89Mods/6507SBC/Programs/psg_test/test.asm

.feature string_escapes
.feature org_per_seg
.feature c_comments

PORT1_OUT = $0201
PORT2_OUT = $0202
PORT_IN   = $0208

mem_start = $80
port1_shadow = mem_start
port2_shadow = mem_start+1
temp = mem_start+2
ptr_lo = mem_start+3
ptr_hi = mem_start+4
temp2 = mem_start+5

.segment "CODE"
NMI:
	rti
IRQ:
	rti
RESET:
	ldx #$FF
	txs
	lda #0
	sta port2_shadow
	sta temp
	
	lda #(vgm_data&255)
	sta ptr_lo
	lda #((vgm_data/256)&255)
	sta ptr_hi
	
	lda #64
	sta PORT1_OUT
	sta port1_shadow
	
	jsr init_psg
	
loop:
	lda port2_shadow
	eor #1
	sta PORT2_OUT
	sta port2_shadow
	ldx #0
	lda (ptr_lo,X)
	cmp #$50
	beq vgm_note
	cmp #$61
	beq vgm_delay
	cmp #$63
	beq vgm_20ms
	cmp #$66
	beq end_song
	jmp end_switch
vgm_note:
	jsr inc_pointer
	lda (ptr_lo,X)
	jsr psg_write
	jmp end_switch
vgm_delay:
	jsr inc_pointer
	lda (ptr_lo,X)
	sta temp
	jsr inc_pointer
	lda (ptr_lo,X)
	sta temp2
	
	lda temp2
	lsr
	sta temp2
	lda temp
	ror
	sta temp
vgm_delay_loop:
	nop
	nop
	nop
	nop
	nop
	nop
	nop
	nop
	nop
	lda temp
	sec
	sbc #1
	sta temp
	lda temp2
	sbc #0
	sta temp2
	lda #0
	ora temp
	ora temp2
	bne vgm_delay_loop
	jmp end_switch
vgm_20ms:
	lda #$72
	sta temp
	lda #$03
	sta temp2
	jmp vgm_delay_loop
end_switch:

	jsr inc_pointer
	jmp loop
	
end_song:
	lda #%11111001
	jsr psg_write
	lda #%11111011
	jsr psg_write
	lda #%11111101
	jsr psg_write
	lda #%11111111
	jsr psg_write
halt:
	nop
	lda #%11111001
	jsr psg_write
	lda port2_shadow
	eor #1
	sta PORT2_OUT
	sta port2_shadow
	lda #31
	jsr long_delay
	lda PORT_IN
	and #1
	bne halt
	jmp RESET
	
inc_pointer:
	lda ptr_lo
	clc
	adc #1
	sta ptr_lo
	lda ptr_hi
	adc #0
	sta ptr_hi
	rts

init_psg:
	lda #%11111001
	jsr psg_write
	lda #%11111011
	jsr psg_write
	lda #%11111101
	jsr psg_write
	lda #%11111111
	jsr psg_write
	
	lda #64
	jsr long_delay
	
	lda #%00110001
	jsr psg_write
	lda #%00100000
	jsr psg_write
	
	lda #%00011001
	jsr psg_write
	lda #16
	jsr long_delay
	lda #%11111001
	jsr psg_write
	lda #4
	jsr long_delay
	lda #%00011001
	jsr psg_write
	lda #16
	jsr long_delay
	lda #%11111001
	jsr psg_write
	
	lda #64
	jsr long_delay
	rts

psg_write:
	pha
	lda port1_shadow
	and #%11110000
	sta port1_shadow
	pla
	pha
	and #%00001111
	ora port1_shadow
	sta PORT1_OUT
	sta port1_shadow
	
	lda port2_shadow
	and #%00001111
	sta port2_shadow
	pla
	and #%11110000
	ora port2_shadow
	sta PORT2_OUT
	sta port2_shadow
	
	lda port1_shadow
	and #%10111111
	sta PORT1_OUT
	nop
	nop
	nop
	nop
	nop
	nop
	ora #%01000000
	sta PORT1_OUT
	sta port1_shadow
	nop
	nop
	nop
	nop
	rts

long_delay:
	jsr delay
	sec
	sbc #1
	bcs long_delay
	rts

delay:
	pha
	lda #0
delay_loop:
	nop
	nop
	nop
	nop
	nop
	nop
	nop
	nop
	nop
	nop
	nop
	nop
	nop
	nop
	nop
	nop
	nop
	nop
	nop
	nop
	nop
	nop
	nop
	clc
	adc #1
	bcc delay_loop
	pla
	rts

vgm_data:
.byte $50, $fd, $61, $17, $00, $50, $cb, $61
.byte $0d, $00, $50, $03, $61, $02, $00, $50
.byte $70, $61, $90, $01, $50, $f9, $61, $0c
.byte $00, $50, $41, $61, $02, $00, $50, $fc
.byte $61, $6e, $41, $50, $cb, $61, $0c, $00
.byte $50, $13, $61, $02, $00, $50, $50, $61
.byte $d9, $44, $50, $cb, $61, $0c, $00, $50
.byte $a3, $61, $02, $00, $50, $90, $61, $d9
.byte $44, $50, $cb, $61, $0c, $00, $50, $a3
.byte $61, $02, $00, $50, $10, $61, $d7, $44
.byte $50, $cd, $61, $0b, $00, $50, $15, $61
.byte $02, $00, $50, $a4, $61, $0a, $00, $50
.byte $cb, $61, $0d, $00, $50, $a3, $61, $02
.byte $00, $50, $90, $61, $8d, $01, $50, $c9
.byte $61, $0b, $00, $50, $21, $61, $02, $00
.byte $50, $1c, $61, $b1, $20, $50, $cd, $61
.byte $0b, $00, $50, $45, $61, $02, $00, $50
.byte $38, $61, $62, $22, $50, $cd, $61, $0b
.byte $00, $50, $a5, $61, $02, $00, $50, $68
.byte $61, $66, $22, $50, $cd, $61, $0b, $00
.byte $50, $35, $61, $02, $00, $50, $48, $61
.byte $69, $22, $50, $cd, $61, $0c, $00, $50
.byte $85, $61, $02, $00, $50, $70, $61, $63
.byte $22, $50, $cd, $61, $0b, $00, $50, $35
.byte $61, $02, $00, $50, $48, $61, $66, $22
.byte $50, $cd, $61, $0b, $00, $50, $a5, $61
.byte $02, $00, $50, $68, $61, $0a, $00, $50
.byte $cb, $61, $0d, $00, $50, $43, $61, $02
.byte $00, $50, $d0, $61, $4b, $22, $50, $cd
.byte $61, $0b, $00, $50, $45, $61, $02, $00
.byte $50, $38, $61, $63, $22, $50, $cd, $61
.byte $0b, $00, $50, $15, $61, $02, $00, $50
.byte $a4, $61, $6a, $22, $50, $cd, $61, $0b
.byte $00, $50, $45, $61, $02, $00, $50, $38
.byte $61, $62, $22, $50, $cd, $61, $0b, $00
.byte $50, $a5, $61, $02, $00, $50, $68, $61
.byte $69, $22, $50, $cd, $61, $0b, $00, $50
.byte $35, $61, $02, $00, $50, $48, $61, $62
.byte $22, $50, $cd, $61, $0c, $00, $50, $85
.byte $61, $02, $00, $50, $70, $61, $0a, $00
.byte $50, $cb, $61, $9d, $01, $50, $c9, $61
.byte $bd, $20, $50, $cd, $61, $0b, $00, $50
.byte $35, $61, $02, $00, $50, $48, $61, $65
.byte $22, $50, $cd, $61, $0b, $00, $50, $a5
.byte $61, $02, $00, $50, $68, $61, $68, $22
.byte $50, $cd, $61, $0b, $00, $50, $45, $61
.byte $02, $00, $50, $38, $61, $63, $22, $50
.byte $cd, $61, $0b, $00, $50, $15, $61, $02
.byte $00, $50, $a4, $61, $0a, $00, $50, $cb
.byte $61, $0c, $00, $50, $03, $61, $02, $00
.byte $50, $70, $61, $4e, $22, $50, $cd, $61
.byte $0b, $00, $50, $45, $61, $02, $00, $50
.byte $38, $61, $67, $22, $50, $cd, $61, $0b
.byte $00, $50, $e5, $61, $02, $00, $50, $84
.byte $61, $0a, $00, $50, $cb, $61, $0c, $00
.byte $50, $13, $61, $02, $00, $50, $50, $61
.byte $4e, $22, $50, $cd, $61, $0b, $00, $50
.byte $45, $61, $02, $00, $50, $38, $61, $64
.byte $22, $50, $cd, $61, $0b, $00, $50, $85
.byte $61, $02, $00, $50, $a8, $61, $0a, $00
.byte $50, $cb, $61, $0c, $00, $50, $a3, $61
.byte $02, $00, $50, $90, $61, $4d, $22, $50
.byte $cd, $61, $0b, $00, $50, $35, $61, $02
.byte $00, $50, $48, $61, $64, $22, $50, $cd
.byte $61, $0b, $00, $50, $35, $61, $02, $00
.byte $50, $08, $61, $0a, $00, $50, $cb, $61
.byte $0c, $00, $50, $a3, $61, $02, $00, $50
.byte $10, $61, $4d, $22, $50, $cd, $61, $0c
.byte $00, $50, $85, $61, $02, $00, $50, $70
.byte $61, $66, $22, $50, $cd, $61, $0b, $00
.byte $50, $15, $61, $02, $00, $50, $a4, $61
.byte $0a, $00, $50, $cb, $61, $0d, $00, $50
.byte $a3, $61, $02, $00, $50, $90, $61, $8e
.byte $01, $50, $c9, $61, $bb, $20, $50, $cd
.byte $61, $0b, $00, $50, $45, $61, $02, $00
.byte $50, $38, $61, $66, $22, $50, $cd, $61
.byte $0b, $00, $50, $a5, $61, $02, $00, $50
.byte $68, $61, $66, $22, $50, $cd, $61, $0b
.byte $00, $50, $35, $61, $02, $00, $50, $48
.byte $61, $69, $22, $50, $cd, $61, $0c, $00
.byte $50, $85, $61, $02, $00, $50, $70, $61
.byte $63, $22, $50, $cd, $61, $0b, $00, $50
.byte $35, $61, $02, $00, $50, $48, $61, $64
.byte $22, $50, $cd, $61, $0b, $00, $50, $a5
.byte $61, $02, $00, $50, $68, $61, $68, $22
.byte $50, $cd, $61, $0b, $00, $50, $45, $61
.byte $02, $00, $50, $38, $61, $66, $22, $50
.byte $cd, $61, $0b, $00, $50, $15, $61, $02
.byte $00, $50, $a4, $61, $66, $22, $50, $cd
.byte $61, $0b, $00, $50, $45, $61, $02, $00
.byte $50, $38, $61, $65, $22, $50, $cd, $61
.byte $0b, $00, $50, $a5, $61, $02, $00, $50
.byte $68, $61, $64, $22, $50, $cd, $61, $0b
.byte $00, $50, $35, $61, $02, $00, $50, $48
.byte $61, $65, $22, $50, $cd, $61, $0c, $00
.byte $50, $85, $61, $02, $00, $50, $70, $61
.byte $0a, $00, $50, $cb, $61, $9e, $01, $50
.byte $c9, $61, $bf, $20, $50, $cd, $61, $0b
.byte $00, $50, $35, $61, $02, $00, $50, $48
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
.byte $01, $50, $f9, $61, $07, $00, $50, $fd
.byte $61, $06, $00, $50, $fd, $61, $07, $00
.byte $50, $fb, $61, $06, $00, $50, $fb, $61
.byte $a3, $01, $50, $f9, $61, $06, $00, $50
.byte $f9, $66

.byte 'E','O','F'

.segment "VECTORS"
.word NMI,RESET,IRQ
