89Mods/6507SBC/Verilog/test_pgm/arith_test.asm

.feature string_escapes
.feature org_per_seg
.feature c_comments

mem_start = $80
min00 = mem_start
min01 = mem_start+1
min02 = mem_start+2
min03 = mem_start+3
min10 = mem_start+4
min11 = mem_start+5
min12 = mem_start+6
min13 = mem_start+7
mres0 = mem_start+8
mres1 = mem_start+9
mres2 = mem_start+10
mres3 = mem_start+11
mres4 = mem_start+12
mres5 = mem_start+13
mres6 = mem_start+14
mres7 = mem_start+15
mtemp0 = mem_start+16
mtemp1 = mem_start+17
mtemp2 = mem_start+18
mtemp3 = mem_start+19
mtemp4 = mem_start+20
mtemp5 = mem_start+21
mtemp6 = mem_start+22
rem0 = mem_start+23
rem1 = mem_start+24
rem2 = mem_start+25
rem3 = mem_start+26

temp0 = mem_start+27

.segment "CODE"
NMI:
	rti
IRQ:
	nop
	lda #'C'
	sta $FFFF
	lda #'h'
	sta $FFFF
	lda #'i'
	sta $FFFF
	lda #'r'
	sta $FFFF
	lda #'p'
	sta $FFFF
	lda #'!'
	sta $FFFF
	lda #10
	sta $FFFF
	lda #13
	sta $FFFF
	nop
	rti
RESET:
	ldx #$FF
	txs
	brk
	
	ldx #0
test_loop_1:
	lda m_ins_8x8,X
	cmp #255
	beq test_loop_1_end
	inx
	jsr print_hex
	sta min00
	lda #'*'
	sta $FFFF
	lda m_ins_8x8,X
	jsr print_hex
	sta min10
	lda #'='
	sta $FFFF
	jsr mul_8x8
	lda mres1
	jsr print_hex
	lda mres0
	jsr print_hex
	lda #10
	sta $FFFF
	lda #13
	sta $FFFF
	inx
	jmp test_loop_1
test_loop_1_end:
	lda #10
	sta $FFFF
	lda #13
	sta $FFFF
	ldx #0
test_loop_2:
	lda div_ins_16x16,X
	sta min01
	cmp #255
	beq test_loop_2_end
	jsr print_hex
	inx
	lda div_ins_16x16,X
	jsr print_hex
	sta min00
	lda #'/'
	inx
	sta $FFFF
	lda div_ins_16x16,X
	jsr print_hex
	sta min11
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
	rol min01
	rol mtemp0
	rol mtemp1
	sec
	lda mtemp0
	sbc min10
	lda mtemp1
	sbc min11
	bcc div_16x16_continue
	sec
	lda mtemp0
	sbc min10
	sta mtemp0
	lda mtemp1
	sbc min11
	sta mtemp1
	inc mres0
div_16x16_continue:
	dec mtemp2
	bne div_16x16_loop
	lda mtemp0
	sta rem0
	lda mtemp1
	sta rem1
	rts

div_32x32:
	lda #0
	sta mres0
	sta mres1
	sta mres2
	sta mres3
	sta mtemp0
	sta mtemp1
	sta mtemp2
	sta mtemp3
	lda #32
	sta mtemp4
div_32x32_loop:
	asl mres0
	rol mres1
	rol mres2
	rol mres3
	
	asl min00
	rol min01
	rol min02
	rol min03
	rol mtemp0
	rol mtemp1
	rol mtemp2
	rol mtemp3
	
	sec
	lda mtemp0
	sbc min10
	lda mtemp1
	sbc min11
	lda mtemp2
	sbc min12
	lda mtemp3
	sbc min13
	bcc div_32x32_continue
	
	sec
	lda mtemp0
	sbc min10
	sta mtemp0
	lda mtemp1
	sbc min11
	sta mtemp1
	lda mtemp2
	sbc min12
	sta mtemp2
	lda mtemp3
	sbc min13
	sta mtemp3
	
	inc mres0
div_32x32_continue:
	dec mtemp4
	bne div_32x32_loop
	
	lda mtemp0
	sta rem0
	lda mtemp1
	sta rem1
	lda mtemp2
	sta rem2
	lda mtemp3
	sta rem3
	
	rts

div_fixed:
	txa
	pha
	lda #0
	sta temp0
	lda min03
	bpl div_fixed_pos_0
	
	sec
	ldx #0
div_fixed_inv_loop_0:
	lda min00,X
	eor #255
	adc #0
	sta min00,X
	inx
	txa
	cmp #4
	bne div_fixed_inv_loop_0
	lda #1
	eor temp0
	sta temp0
	
div_fixed_pos_0:
	lda min13
	bpl div_fixed_pos_1
	
	sec
	ldx #0
div_fixed_inv_loop_1:
	lda min10,X
	eor #255
	adc #0
	sta min10,X
	inx
	txa
	cmp #4
	bne div_fixed_inv_loop_1
	lda #1
	eor temp0
	sta temp0
	
div_fixed_pos_1:
	
	lda #0
	sta mres0
	sta mres1
	sta mres2
	sta mres3
	sta mtemp0
	sta mtemp1
	sta mtemp2
	sta mtemp3
	lda #56
	sta mtemp4
div_fixed_loop:
	asl mres0
	rol mres1
	rol mres2
	rol mres3
	
	asl min00
	rol min01
	rol min02
	rol min03
	rol mtemp0
	rol mtemp1
	rol mtemp2
	rol mtemp3
	
	sec
	lda mtemp0
	sbc min10
	lda mtemp1
	sbc min11
	lda mtemp2
	sbc min12
	lda mtemp3
	sbc min13
	bcc div_fixed_continue
	
	sec
	lda mtemp0
	sbc min10
	sta mtemp0
	lda mtemp1
	sbc min11
	sta mtemp1
	lda mtemp2
	sbc min12
	sta mtemp2
	lda mtemp3
	sbc min13
	sta mtemp3
	
	inc mres0
div_fixed_continue:
	dec mtemp4
	bne div_fixed_loop
	
	lda temp0
	beq div_fixed_pos_2
	
	sec
	ldx #0
div_fixed_inv_loop_2:
	lda mres0,X
	eor #255
	adc #0
	sta mres0,X
	inx
	txa
	cmp #4
	bne div_fixed_inv_loop_2
	
div_fixed_pos_2:
	pla
	tax
	rts

print_num_divs:
	.dword 1
	.dword 10
	.dword 100
	.dword 1000
	.dword 10000
	.dword 100000
	.dword 1000000
	.dword 10000000
	.dword 100000000
	.dword 1000000000
print_num:
	txa
	pha
	tya
	pha
	lda min03
	bpl print_num_pos
	lda #'-'
	sta $FFFF
	sec
	ldx #4
	ldy #0
print_num_inv_loop_0:
	lda min00,Y
	eor #$FF
	adc #0
	sta min00,Y
	iny
	dex
	bne print_num_inv_loop_0
print_num_pos:
	lda #0
	sta temp0
	ldx #10
print_num_loop:
	dex
	
	txa
	asl
	asl
	tay
	
	lda print_num_divs,Y
	sta min10
	iny
	lda print_num_divs,Y
	sta min11
	iny
	lda print_num_divs,Y
	sta min12
	iny
	lda print_num_divs,Y
	sta min13
	
	jsr div_32x32
	lda temp0
	bne print_num_print
	lda mres0
	bne print_num_print
	txa
	beq print_num_print
	jmp print_num_noprint
print_num_print:
	lda mres0
	clc
	adc #'0'
	sta $FFFF
	sta temp0
print_num_noprint:
	lda rem0
	sta min00
	lda rem1
	sta min01
	lda rem2
	sta min02
	lda rem3
	sta min03
	txa
	bne print_num_loop
	
	pla
	tay
	pla
	tax
	rts

print_fixed:
	txa
	pha
	tya
	pha
	lda min03
	bpl print_fixed_pos
	lda #'-'
	sta $FFFF
	sec
	ldx #4
	ldy #0
print_fixed_inv_loop_0:
	lda min00,Y
	eor #$FF
	adc #0
	sta min00,Y
	iny
	dex
	bne print_fixed_inv_loop_0
print_fixed_pos:
	lda min02
	pha
	lda min01
	pha
	lda min00
	pha
	lda min03
	sta min00
	lda #0
	sta min01
	sta min02
	sta min03
	jsr print_num
	lda #'.'
	sta $FFFF
	lda #0
	sta min03
	pla
	sta min00
	pla
	sta min01
	pla
	sta min02
	
	ldx #8
	lda #10
	sta min13
	lda #0
	sta min12
	sta min11
	sta min10
print_fixed_loop:
	jsr mul_fixed
	lda mres3
	clc
	adc #'0'
	sta $FFFF
	lda mres2
	sta min02
	lda mres1
	sta min01
	lda mres0
	sta min00
	dex
	bne print_fixed_loop
	
	pla
	tay
	pla
	tax
	rts

print_hex:
	sta temp0
	tya
	pha
	lda temp0
	pha
	ror
	ror
	ror
	ror
	and #15
	tay
	lda hex_digits,Y
	sta $FFFF
	pla
	and #15
	tay
	lda hex_digits,Y
	sta $FFFF
	pla
	tay
	lda temp0
	rts
	
m_ins_8x8:
.byte 5,6,57,8,233,108,0,3,25,8,255
div_ins_16x16:
.byte 1,33,0,25
.byte 23,78,3,108
.byte 0,28,1,1
.byte 200,55,0,0
.byte 0,8,0,2
.byte 0,2,200,55
.byte 200,55,0,88
.byte 255
mul_ins_32x32:
.byte 0,0,37,200,0,0,245,99
.byte 0,23,57,68,0,0,88,69
.byte 55,29,87,33,229,1,58,108
.byte 0,0,0,0,23,158,10,58
.byte 0,0,0,55,23,158,10,58
.byte 0,23,57,68,0,0,0,0
.byte 255
div_ins_32x32:
.byte 0,0,0,200,0,0,0,50
.byte 27,38,201,208,0,29,31,0
.byte 108,37,19,111,33,11,60,183
.byte 108,37,19,111,0,0,0,0
.byte 0,0,0,0,33,11,60,183
.byte 18,91,102,111,0,37,131,19
.byte 255
print_num_ins:
.dword 37222
.dword 27888576
.dword 1768900378
.dword 1
.dword 0
.dword $FFFFFFFB
.byte 255
hex_digits:
.asciiz "0123456789ABCDEF"
	
.byte 'E','O','F'

.segment "VECTORS"
.word NMI,RESET,IRQ
